Snow014/M_IAQ/Photos/20250118_133801.jpg

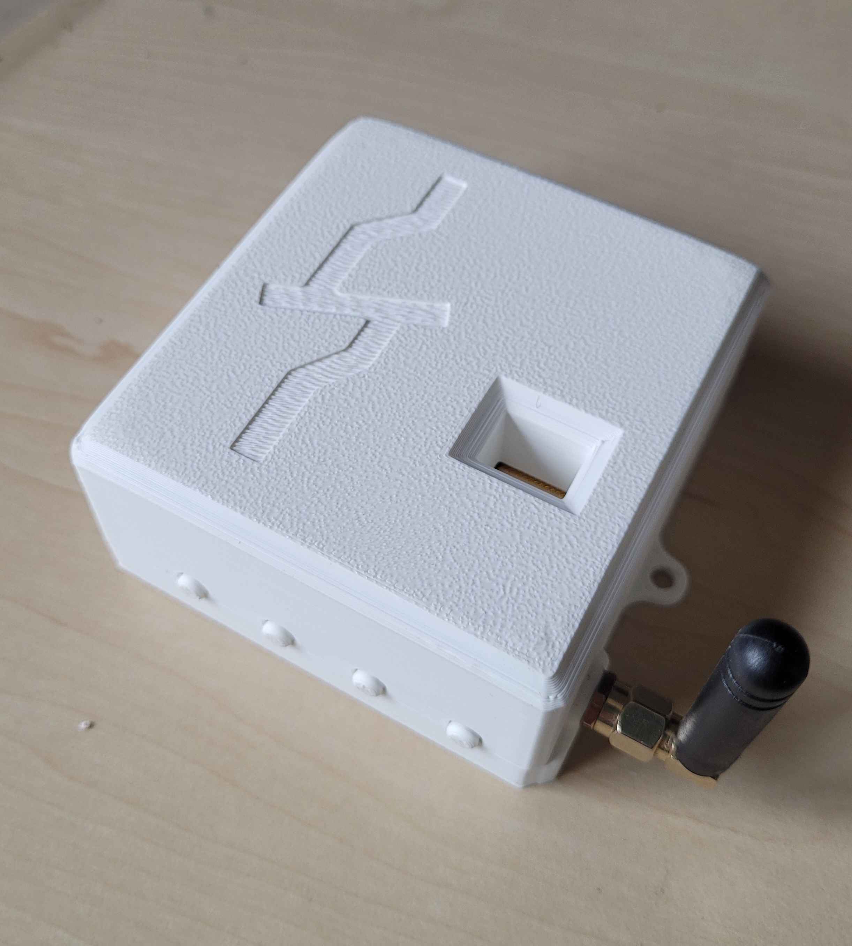
Photos/20250118_133801.jpg
