Snow014/M_IAQ/Photos/20250118_133805.jpg

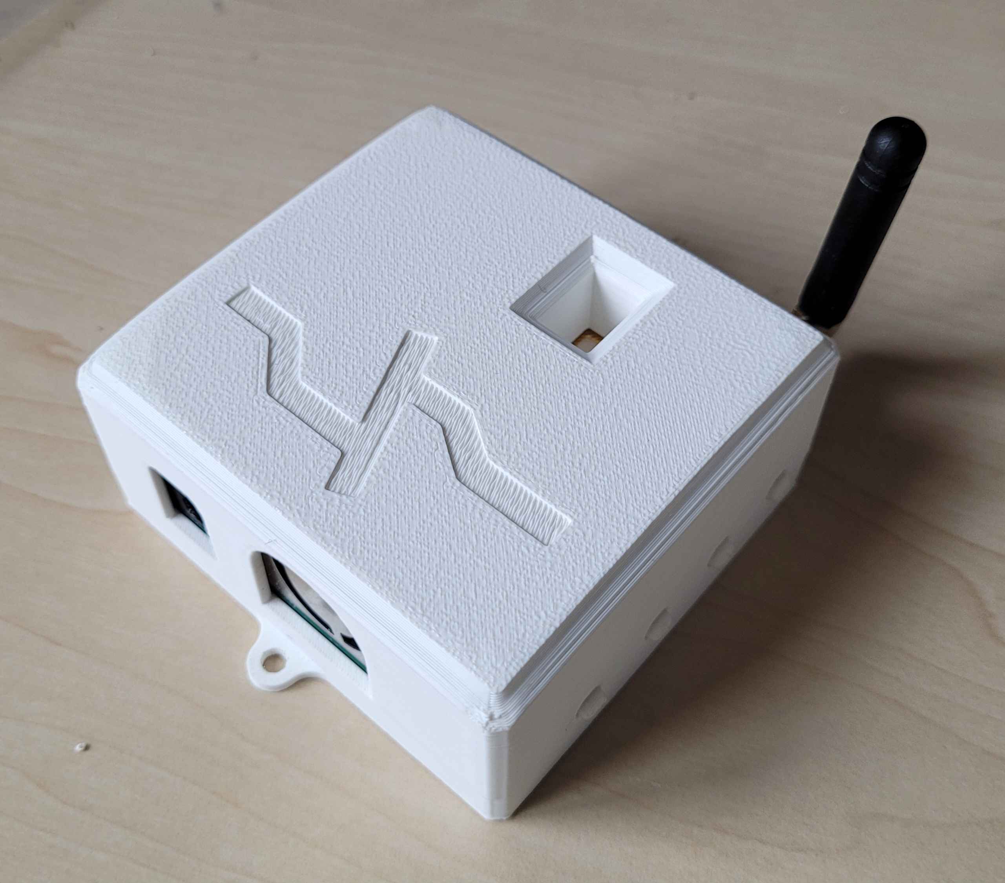
Photos/20250118_133805.jpg
