Snow014/M_IAQ/Photos/20250118_134000.jpg

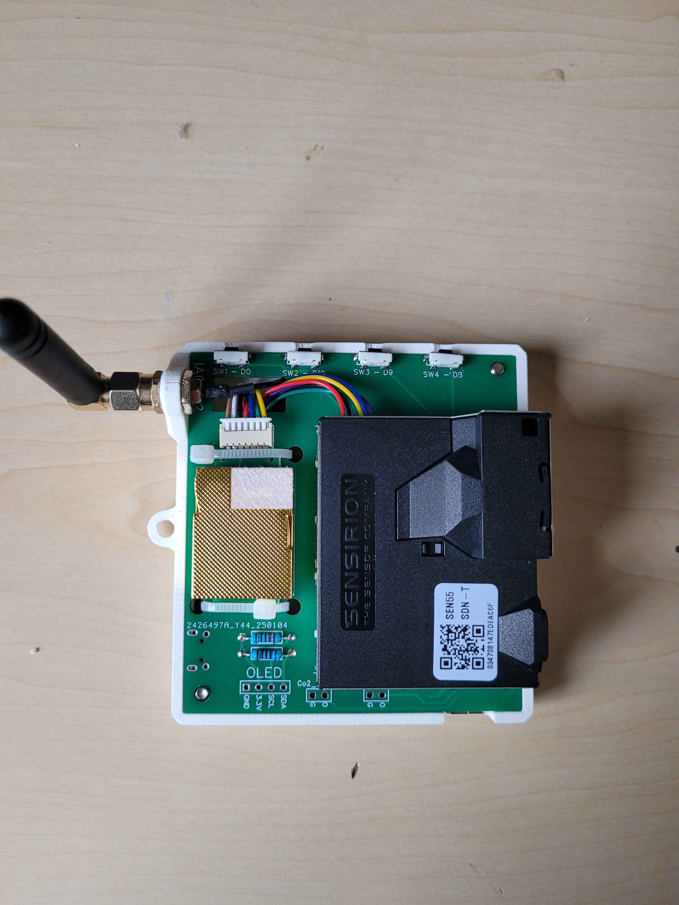
Photos/20250118_134000.jpg
