Snow014/M_IAQ/Photos/20250118_134018.jpg

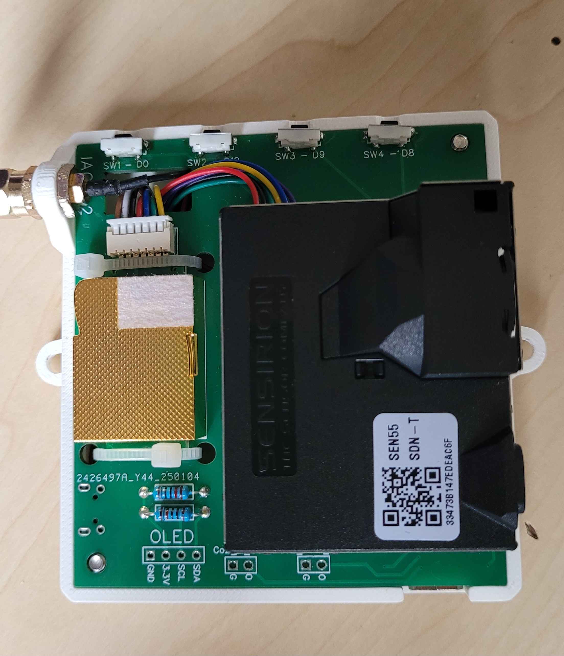
Photos/20250118_134018.jpg
